nicka06/Glasses-V.01/production/pics/Screenshot 2025-07-20 at 12.17.45 PM.png

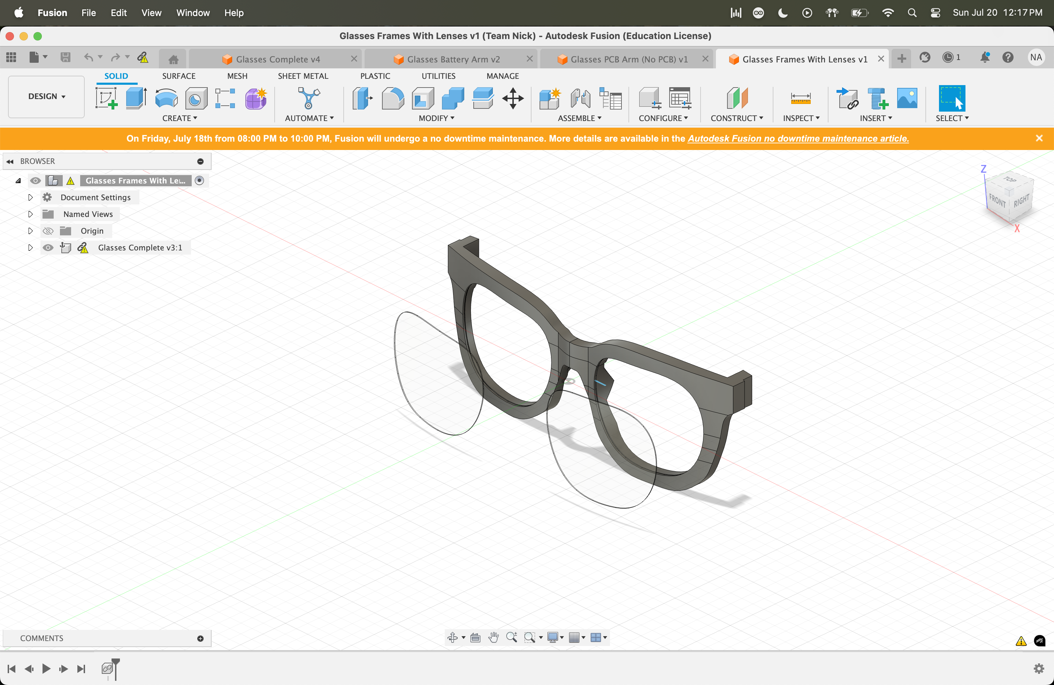
production/pics/Screenshot 2025-07-20 at 12.17.45 PM.png
